MOSH-Insa-Toulouse/-MOSH-Insa-Toulouse-2023-2024-4GP-Bresson-Ronne/LTspice/capteur.asc

C1: cap; 100n
C2: cap; 100n
C3: cap; 1µ
C4: cap; 100n
C5: cap; 1p
R1: res; 1k
R2: res; 100k
R3: res; 10k
R4: res; 100k
R5: res; 1k
U1: LTC1050
V1: voltage; 5
V2: voltage; PULSE(0 1 0.2 0.1 0.1 20)
V3: voltage; SINE(0 325 50)
X1: capteurgraphite
Named nets: 0, ADC
.param G0 10n
.param G1 10n
.tran 2
.param R2 100k
