MOSH-Insa-Toulouse/-MOSH-Insa-Toulouse-2023-2024-4GP-Bresson-Ronne/LTspice/capteurgraphite.asc

B1: bi; I=V({G0}+(v(gc,gn)*{G1})
C1: cap; 200µ
R1: res; 1k
Named nets: cp, cn, gn, gp, gc
